ctranstrum/patagona/cases/chaski/top_dovetail.stl

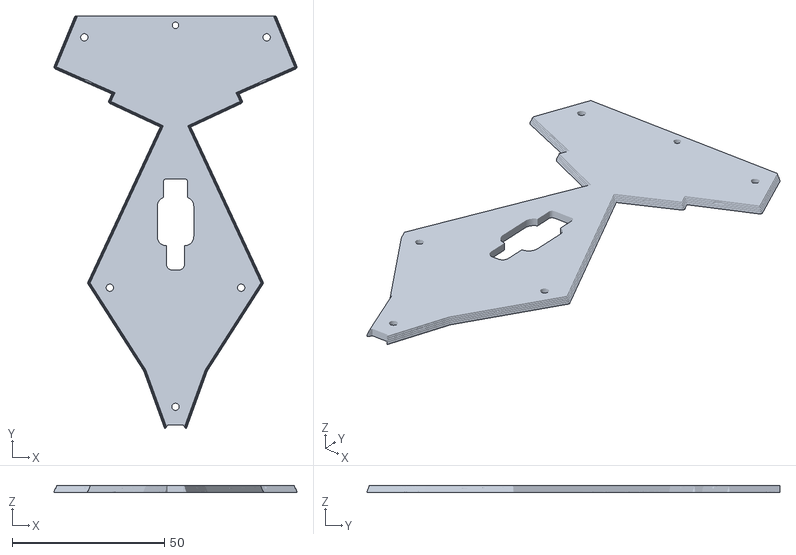
[picture p19: CAD file, 2026-06-06]
cases/chaski/top_dovetail.stl
79.9 x 135.8 x 2.20
