ctranstrum/patagona/cases/gigas/rectangle_bottom_case.stl

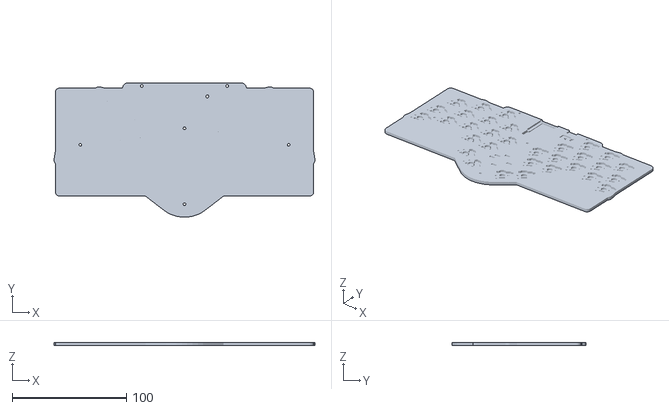
[picture p20: CAD file, 2026-06-06]
cases/gigas/rectangle_bottom_case.stl
228.8 x 117.7 x 3.00
