ctranstrum/patagona/cases/chaski/top_dovetail_left_3.stl

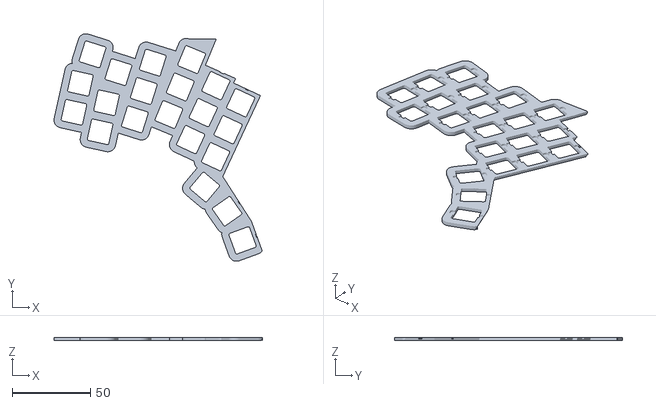
[picture p21: CAD file, 2026-06-06]
cases/chaski/top_dovetail_left_3.stl
161.5 x 145.2 x 2.20
