ctranstrum/patagona/cases/chaski/battery_cover.stl

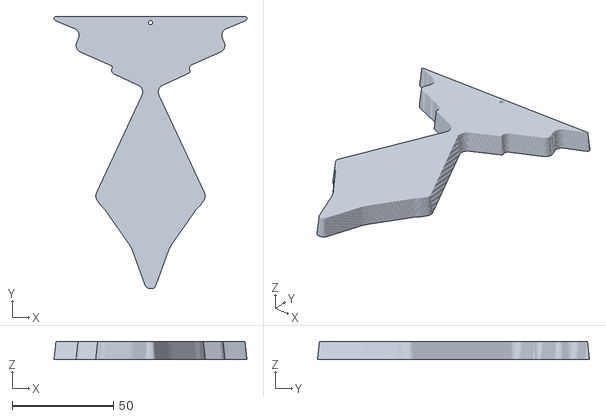
[picture p22: CAD file, 2026-06-06]
cases/chaski/battery_cover.stl
95.4 x 134.5 x 9.00
