ctranstrum/patagona/cases/gigas/top_dovetail_right_1.stl

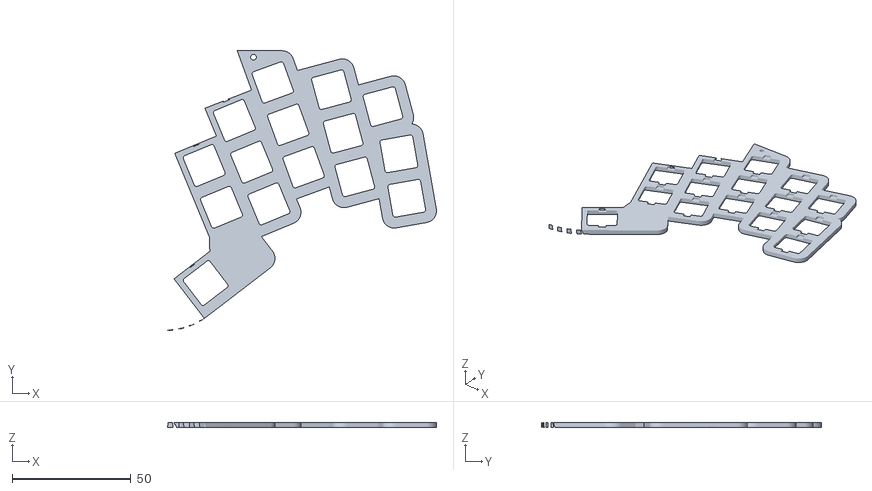
[picture p23: CAD file, 2026-06-06]
cases/gigas/top_dovetail_right_1.stl
160.8 x 117.7 x 2.20
