ctranstrum/patagona/cases/chaski/bottom_case.stl

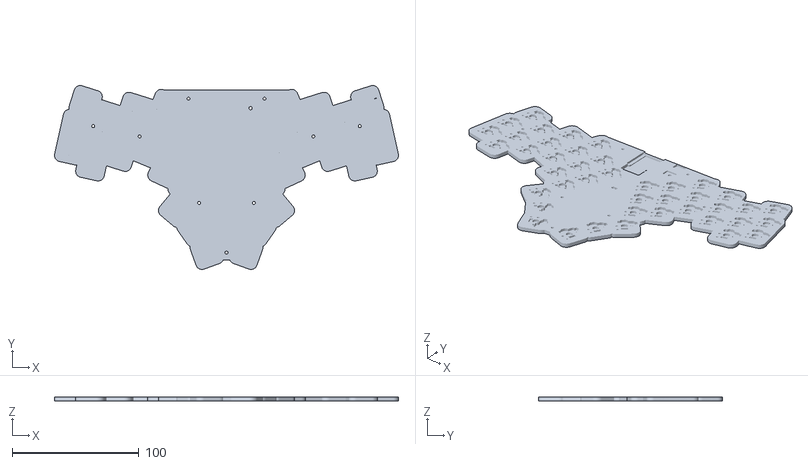
[picture p24: CAD file, 2026-06-06]
cases/chaski/bottom_case.stl
271.6 x 145.2 x 3.00
