ctranstrum/patagona/cases/gigas/top_dovetail_left_2.stl

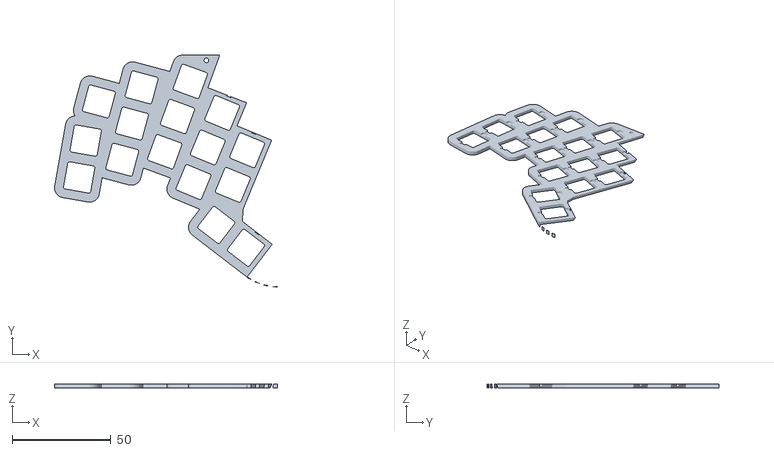
[picture p25: CAD file, 2026-06-06]
cases/gigas/top_dovetail_left_2.stl
163.9 x 117.7 x 2.20
