ctranstrum/patagona/cases/chaski/top_dovetail_right_2.stl

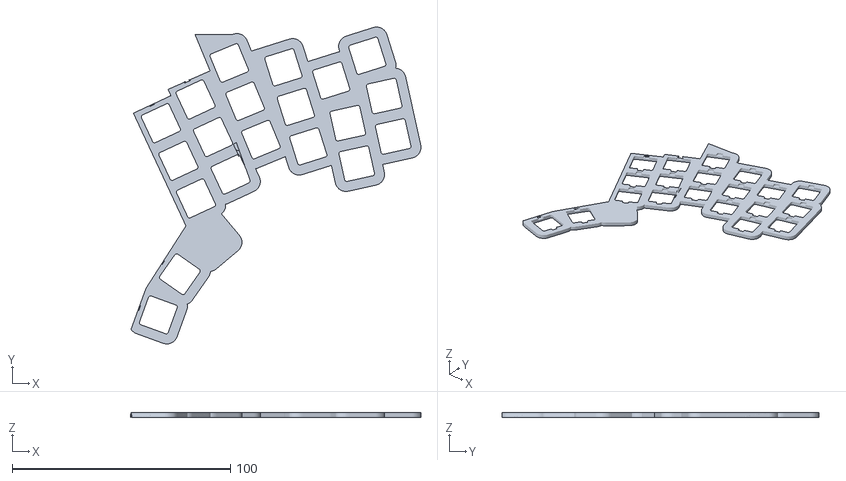
[picture p26: CAD file, 2026-06-06]
cases/chaski/top_dovetail_right_2.stl
168.2 x 145.2 x 2.20
