ctranstrum/patagona/cases/chaski/top_dovetail_right_3.stl

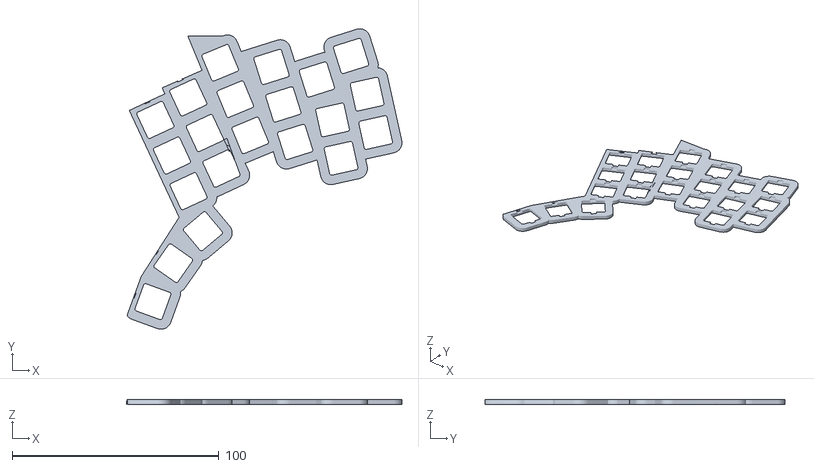
[picture p27: CAD file, 2026-06-06]
cases/chaski/top_dovetail_right_3.stl
168.2 x 145.2 x 2.20
