ctranstrum/patagona/cases/gigas/top_dovetail.stl

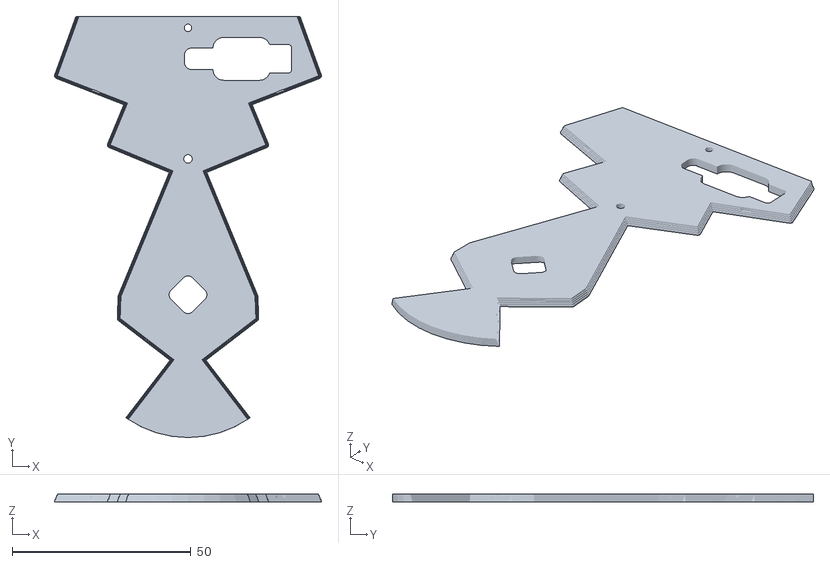
[picture p28: CAD file, 2026-06-06]
cases/gigas/top_dovetail.stl
74.7 x 117.8 x 2.20
